Tomnwol/Drone_Robotech/Emitter/QT_Controller/moc_controller.cpp

/****************************************************************************
** Meta object code from reading C++ file 'controller.hpp'
**
** Created by: The Qt Meta Object Compiler version 68 (Qt 6.8.3)
**
** WARNING! All changes made in this file will be lost!
*****************************************************************************/

#include "controller.hpp"
#include <QtCore/qmetatype.h>

#include <QtCore/qtmochelpers.h>

#include <memory>


#include <QtCore/qxptype_traits.h>
#if !defined(Q_MOC_OUTPUT_REVISION)
#error "The header file 'controller.hpp' doesn't include <QObject>."
#elif Q_MOC_OUTPUT_REVISION != 68
#error "This file was generated using the moc from 6.8.3. It"
#error "cannot be used with the include files from this version of Qt."
#error "(The moc has changed too much.)"
#endif

#ifndef Q_CONSTINIT
#define Q_CONSTINIT
#endif

QT_WARNING_PUSH
QT_WARNING_DISABLE_DEPRECATED
QT_WARNING_DISABLE_GCC("-Wuseless-cast")
namespace {
struct qt_meta_tag_ZN10ControllerE_t {};
} // unnamed namespace


#ifdef QT_MOC_HAS_STRINGDATA
static constexpr auto qt_meta_stringdata_ZN10ControllerE = QtMocHelpers::stringData(
    "Controller",
    "readController",
    ""
);
#else  // !QT_MOC_HAS_STRINGDATA
#error "qtmochelpers.h not found or too old."
#endif // !QT_MOC_HAS_STRINGDATA

Q_CONSTINIT static const uint qt_meta_data_ZN10ControllerE[] = {

 // content:
      12,       // revision
       0,       // classname
       0,    0, // classinfo
       1,   14, // methods
       0,    0, // properties
       0,    0, // enums/sets
       0,    0, // constructors
       0,       // flags
       0,       // signalCount

 // slots: name, argc, parameters, tag, flags, initial metatype offsets
       1,    0,   20,    2, 0x08,    1 /* Private */,

 // slots: parameters
    QMetaType::Void,

       0        // eod
};

Q_CONSTINIT const QMetaObject Controller::staticMetaObject = { {
    QMetaObject::SuperData::link<QObject::staticMetaObject>(),
    qt_meta_stringdata_ZN10ControllerE.offsetsAndSizes,
    qt_meta_data_ZN10ControllerE,
    qt_static_metacall,
    nullptr,
    qt_incomplete_metaTypeArray<qt_meta_tag_ZN10ControllerE_t,
        // Q_OBJECT / Q_GADGET
        QtPrivate::TypeAndForceComplete<Controller, std::true_type>,
        // method 'readController'
        QtPrivate::TypeAndForceComplete<void, std::false_type>
    >,
    nullptr
} };

void Controller::qt_static_metacall(QObject *_o, QMetaObject::Call _c, int _id, void **_a)
{
    auto *_t = static_cast<Controller *>(_o);
    if (_c == QMetaObject::InvokeMetaMethod) {
        switch (_id) {
        case 0: _t->readController(); break;
        default: ;
        }
    }
    (void)_a;
}

const QMetaObject *Controller::metaObject() const
{
    return QObject::d_ptr->metaObject ? QObject::d_ptr->dynamicMetaObject() : &staticMetaObject;
}

void *Controller::qt_metacast(const char *_clname)
{
    if (!_clname) return nullptr;
    if (!strcmp(_clname, qt_meta_stringdata_ZN10ControllerE.stringdata0))
        return static_cast<void*>(this);
    return QObject::qt_metacast(_clname);
}

int Controller::qt_metacall(QMetaObject::Call _c, int _id, void **_a)
{
    _id = QObject::qt_metacall(_c, _id, _a);
    if (_id < 0)
        return _id;
    if (_c == QMetaObject::InvokeMetaMethod) {
        if (_id < 1)
            qt_static_metacall(this, _c, _id, _a);
        _id -= 1;
    }
    if (_c == QMetaObject::RegisterMethodArgumentMetaType) {
        if (_id < 1)
            *reinterpret_cast<QMetaType *>(_a[0]) = QMetaType();
        _id -= 1;
    }
    return _id;
}
QT_WARNING_POP
