Tomnwol/Drone_Robotech/main/UDP_reception.cpp

#include "UDP_reception.hpp"
#include <WiFi.h>
#include <WiFiUdp.h>

const char* ssid = "ESP32_Tom";
const char* password = "12345678";

WiFiUDP udp;
const int udpPort = 4210;

uint8_t payload[22]; // comme NRF_Payload

unsigned long udp_last_time = 0;
unsigned long udp_delta_time = 0;

uint16_t joyThrottle = 0; //analogRead(A0);
int16_t joyYaw = 0;
int16_t joyRoll = 0;
int16_t joyPitch = 0;
uint16_t GP_Pot = 0;
uint8_t SWFailSafe = 0;
uint8_t SWKillSwitch = 0;
float QT_KP = 0;
float QT_KI = 0;
float QT_KD = 0;
uint8_t offsetMotorFL = 0;
uint8_t offsetMotorFR = 0;
uint8_t offsetMotorBL = 0;
uint8_t offsetMotorBR = 0;

//Emmit data from ESP to PC
IPAddress pcIP;
uint16_t pcPort = 0;

void setupUDP() {
    WiFi.mode(WIFI_AP);
    WiFi.softAP(ssid, password, 6);  // canal fixe
    WiFi.setSleep(false);            // désactive power save
    Serial.print("IP ESP32 : ");
    Serial.println(WiFi.softAPIP());

    udp.begin(udpPort);
    Serial.println("UDP en écoute...");
    udp_last_time = millis();
}

uint16_t readBatteryMV() {
    int raw = analogRead(BATTERY_PIN);

    // Converti ADC (0-4095) en mV (supposons 3.3V référence)
    float voltage = (raw / 4095.0) * 3300; // en mV
    return (uint16_t)voltage;
}

uint8_t batteryPercentage() {
    uint16_t mv = readBatteryMV();

    // Contrainte entre min/max
    if (mv >= BATTERY_MAX) return 100;
    if (mv <= BATTERY_MIN) return 0;

    // Map 1910–2320 mV → 0–100 %
    float perc = ((float)(mv - BATTERY_MIN)) / (BATTERY_MAX - BATTERY_MIN) * 100.0;
    return (uint8_t)perc;
}

void sendTelemetry(uint8_t batteryVoltage, int16_t yaw_telemetry, int16_t roll_telemetry,int16_t pitch_telemetry,uint16_t MOT_FL_telemetry, uint16_t MOT_FR_telemetry, uint16_t MOT_BR_telemetry, uint16_t MOT_BL_telemetry) {
    if (pcPort != 0) {
        udp.beginPacket(pcIP, pcPort);
        uint8_t buf[15];
        buf[0] = batteryVoltage;
        buf[1] = yaw_telemetry & 0xFF;
        buf[2] = (yaw_telemetry >> 8) & 0xFF;
        buf[3] = roll_telemetry & 0xFF;
        buf[4] = (roll_telemetry >> 8) & 0xFF;
        buf[5] = pitch_telemetry & 0xFF;
        buf[6] = (pitch_telemetry >> 8) & 0xFF;
        buf[7] = MOT_FL_telemetry & 0xFF;
        buf[8] = (MOT_FL_telemetry >> 8) & 0xFF;
        buf[9] = MOT_FR_telemetry & 0xFF;
        buf[10] = (MOT_FR_telemetry >> 8) & 0xFF;
        buf[11] = MOT_BR_telemetry & 0xFF;
        buf[12] = (MOT_BR_telemetry >> 8) & 0xFF;
        buf[13] = MOT_BL_telemetry & 0xFF;
        buf[14] = (MOT_BL_telemetry >> 8) & 0xFF;

        udp.write(buf, 15);
        udp.endPacket();
    }
}


void handleSendTelemetry(Euler att_telemetry, uint16_t MOT_FL_telemetry, uint16_t MOT_FR_telemetry, uint16_t MOT_BR_telemetry, uint16_t MOT_BL_telemetry){
    static unsigned long lastSend = 0;
    if (millis() - lastSend > 100) {
        lastSend = millis();
        uint8_t value = batteryPercentage(); // Lis la valeur de la batterie ( entre 2,32V et 1,91)
        int16_t yaw_telemetry = (int16_t)(att_telemetry.yaw * 180.0f / M_PI);
        int16_t roll_telemetry = (int16_t)(att_telemetry.roll * 180.0f / M_PI);
        int16_t pitch_telemetry = (int16_t)(att_telemetry.pitch * 180.0f / M_PI);
        sendTelemetry(value, yaw_telemetry, roll_telemetry, pitch_telemetry, MOT_FL_telemetry, MOT_FR_telemetry, MOT_BR_telemetry, MOT_BL_telemetry);
    }
}




void readUDPData() {

    udp_delta_time = millis() - udp_last_time;

    int packetSize;
    uint8_t lastPayload[22];
    bool newPacket = false;

    while ((packetSize = udp.parsePacket()) > 0) {

        if (packetSize == 22) {

            udp.read(lastPayload, 22);
            newPacket = true;

        } else {
            udp.flush();
        }
    }

    // Après avoir vidé le buffer → on utilise uniquement le dernier
    if (newPacket) {

        udp_last_time = millis();

        memcpy(payload, lastPayload, 22);

        pcIP = udp.remoteIP();
        pcPort = udp.remotePort();

        joyThrottle = payload[0] + (payload[1]<<8);
        joyYaw = (int16_t)((uint16_t)payload[2] | ((uint16_t)payload[3] << 8));
        joyRoll = (int16_t)((uint16_t)payload[4] | ((uint16_t)payload[5] << 8));
        joyPitch = (int16_t)((uint16_t)payload[6] | ((uint16_t)payload[7] << 8));
        GP_Pot      = payload[8] + (payload[9]<<8);
        SWFailSafe  = payload[10];
        SWKillSwitch= payload[11];
        QT_KP       = ((float)(uint16_t)(payload[12] + (payload[13]<<8))/100.0);
        QT_KI       = ((float)(uint16_t)(payload[14] + (payload[15]<<8))/100.0);
        QT_KD       = ((float)(uint16_t)(payload[16] + (payload[17]<<8))/100.0);

        offsetMotorFL = payload[18];
        offsetMotorFR = payload[19];
        offsetMotorBL = payload[20];
        offsetMotorBR = payload[21];
    }
}
