Tomnwol/Drone_Robotech/main/utils.hpp

#ifndef __UTILS__H
#define __UTILS__H
#include <Arduino.h> //uint
#include "types.hpp"

float passe_bas(float value, float last_filtered_value, float dt, float w0);
void fill_tab(float * tab, int size_tab);
float mean_tab(float * tab, int size_tab);
void fill_queue(float * tab, int size_tab, float valeur);
Vector3f up_vector(float q0, float q1, float q2, float q3);

//Quaternions
Quaternion quat_conjugate(Quaternion q);
Quaternion quat_multiply(Quaternion q1, Quaternion q2);
Vector3f quat_to_attitude_error(Quaternion q_err);
Vector3f vec_scale(Vector3f v, float s);
Vector3f vec_add(Vector3f v1, Vector3f v2);
Vector3f vec_sub(Vector3f v1, Vector3f v2);
Vector3f vec_clamp(Vector3f value, Vector3f min, Vector3f max);
float float_clamp(float value, float min, float max);
uint16_t int_clamp(uint16_t value, uint16_t min, uint16_t max);
uint8_t uint8_clamp(uint8_t value, uint8_t min, uint8_t max);
float float_remap(float x, float in_min, float in_max, float out_min, float out_max);
Euler quat_to_euler(Quaternion q);
float slew_limit(float target, float prev, float slew_rate, float dt); 
float throttle_curve(float in, float expo);
#endif
